NandhaKishorM/AI-Quadruped-Robot-For-Agriculture/screenshots/img5.gif

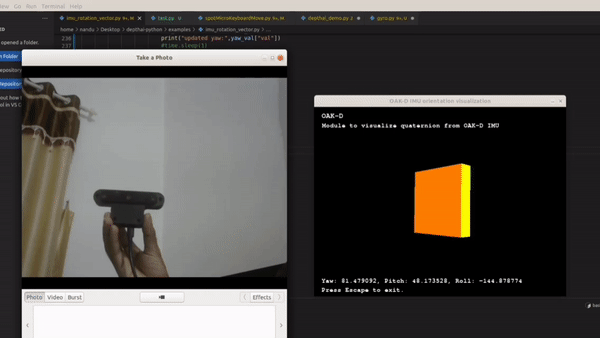
screenshots/img5.gif
