NandhaKishorM/AI-Quadruped-Robot-For-Agriculture/src/assets/1_robot_right_links.png

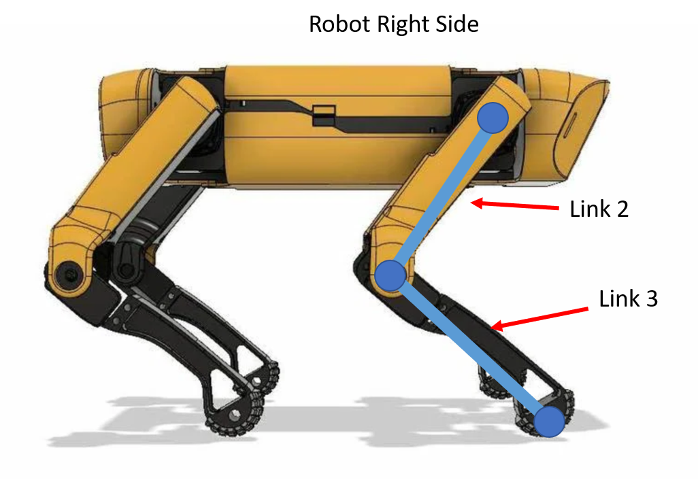
src/assets/1_robot_right_links.png
