NandhaKishorM/AI-Quadruped-Robot-For-Agriculture/src/assets/2_right_straight_links.png

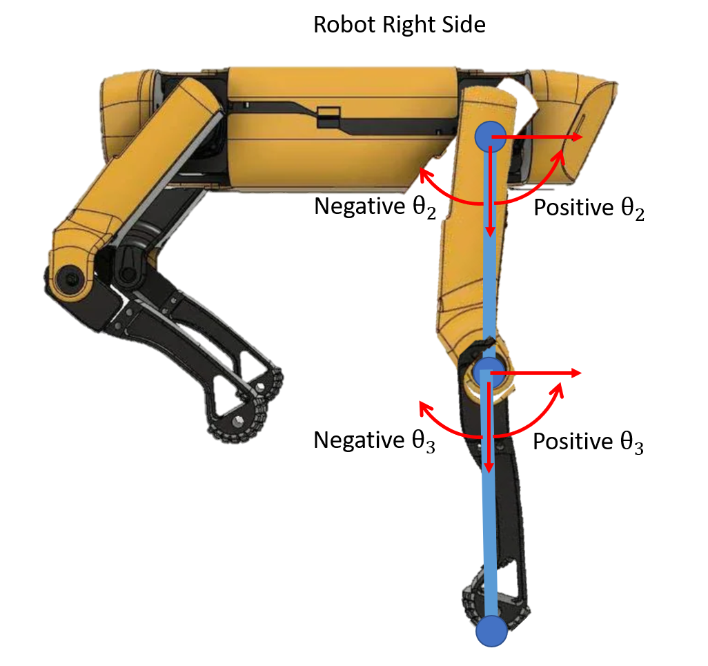
src/assets/2_right_straight_links.png
