NandhaKishorM/AI-Quadruped-Robot-For-Agriculture/src/assets/3_right_link_angles_example.png

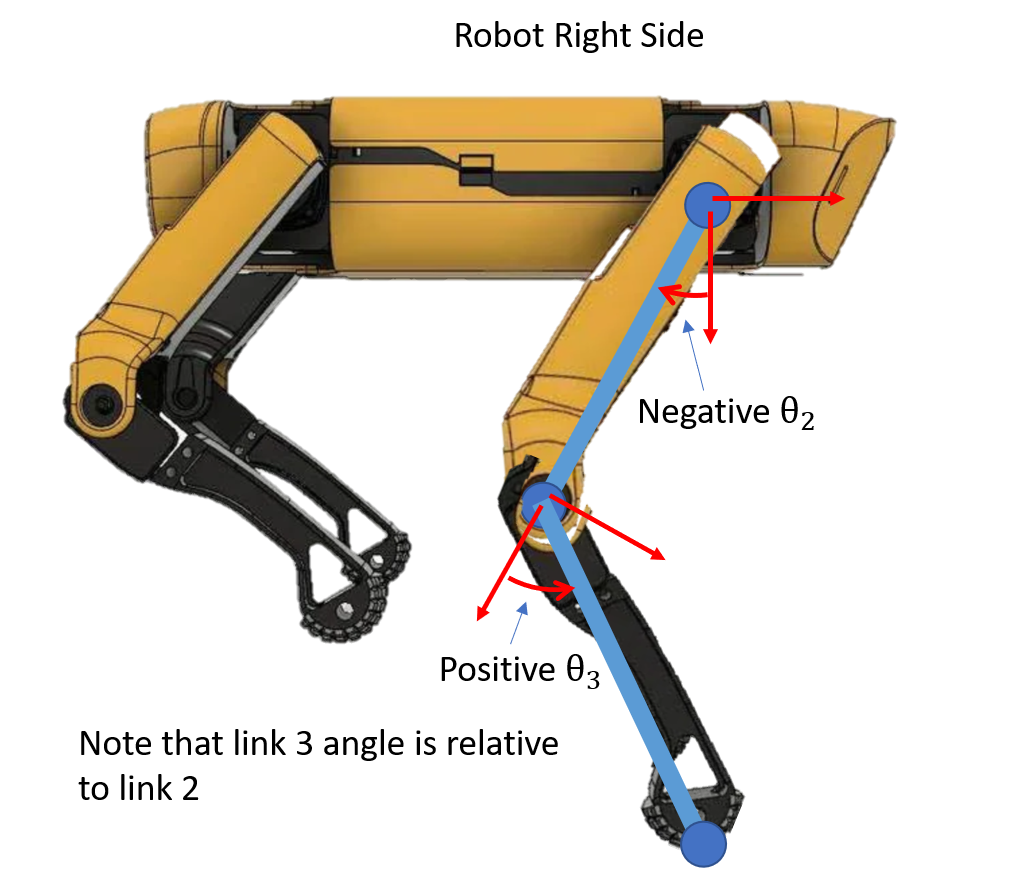
src/assets/3_right_link_angles_example.png
