NandhaKishorM/AI-Quadruped-Robot-For-Agriculture/src/assets/7_robot_left_overview.png

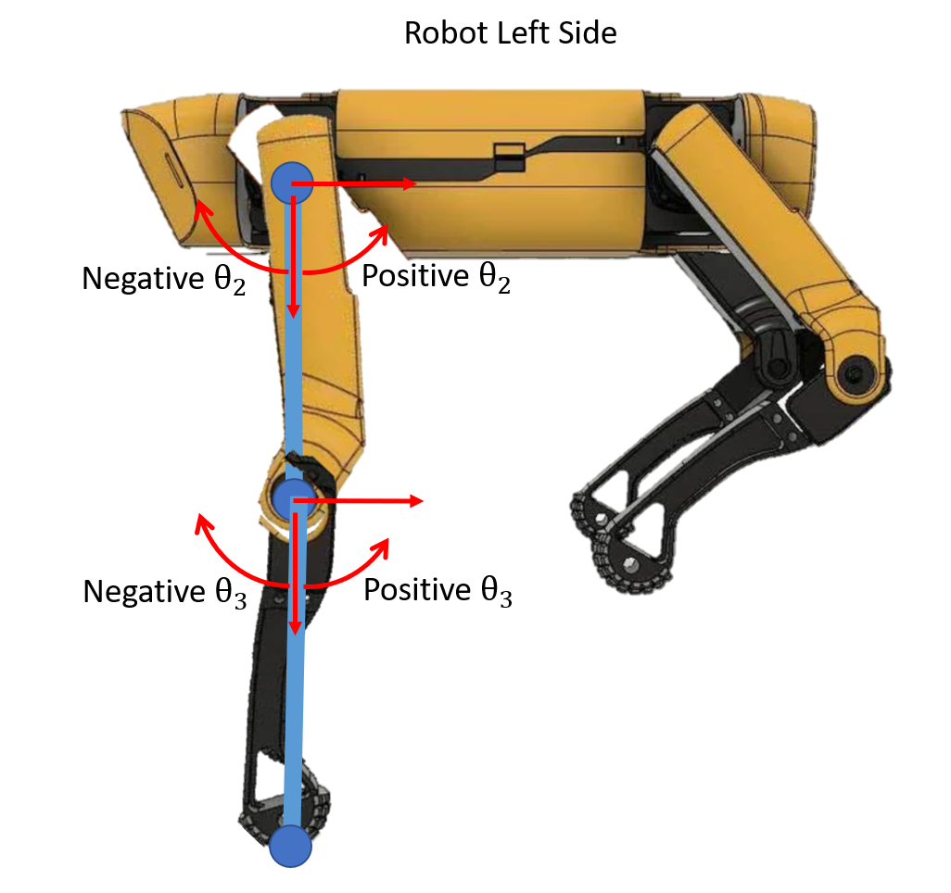
src/assets/7_robot_left_overview.png
