NandhaKishorM/AI-Quadruped-Robot-For-Agriculture/src/assets/12_robot_back_overview.png

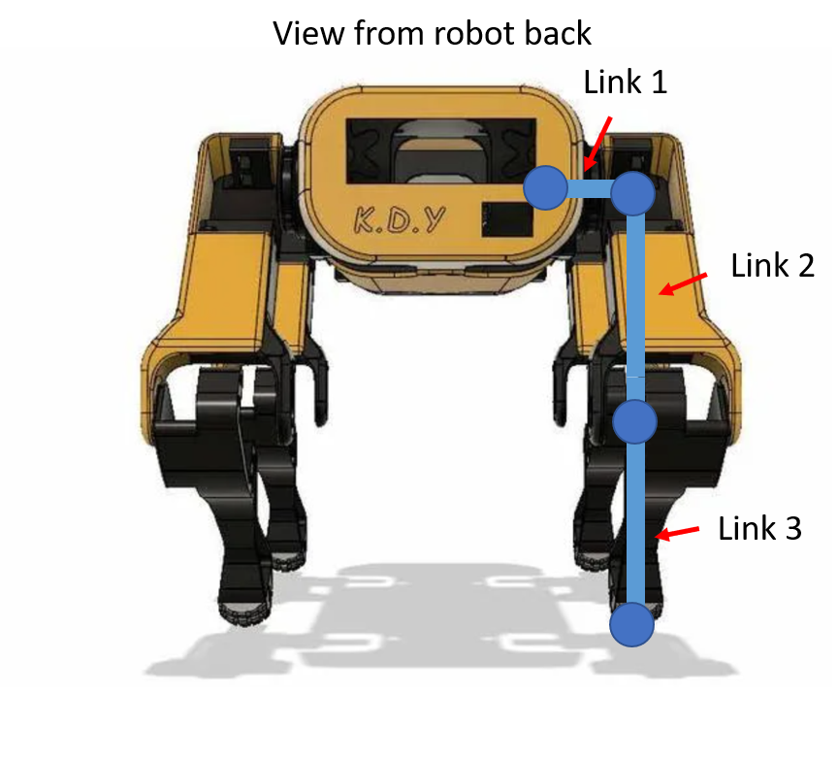
src/assets/12_robot_back_overview.png
