NandhaKishorM/AI-Quadruped-Robot-For-Agriculture/src/assets/kinematic_coord_system.jpg

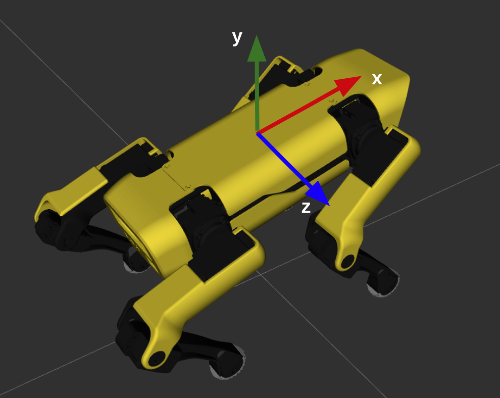
src/assets/kinematic_coord_system.jpg
