NandhaKishorM/AI-Quadruped-Robot-For-Agriculture/src/assets/lidar_mount.jpg

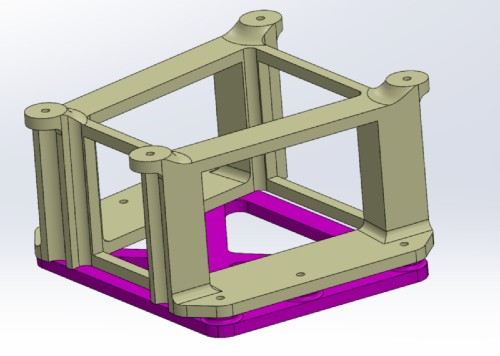
src/assets/lidar_mount.jpg
