NandhaKishorM/AI-Quadruped-Robot-For-Agriculture/src/assets/robot_bottom.jpg

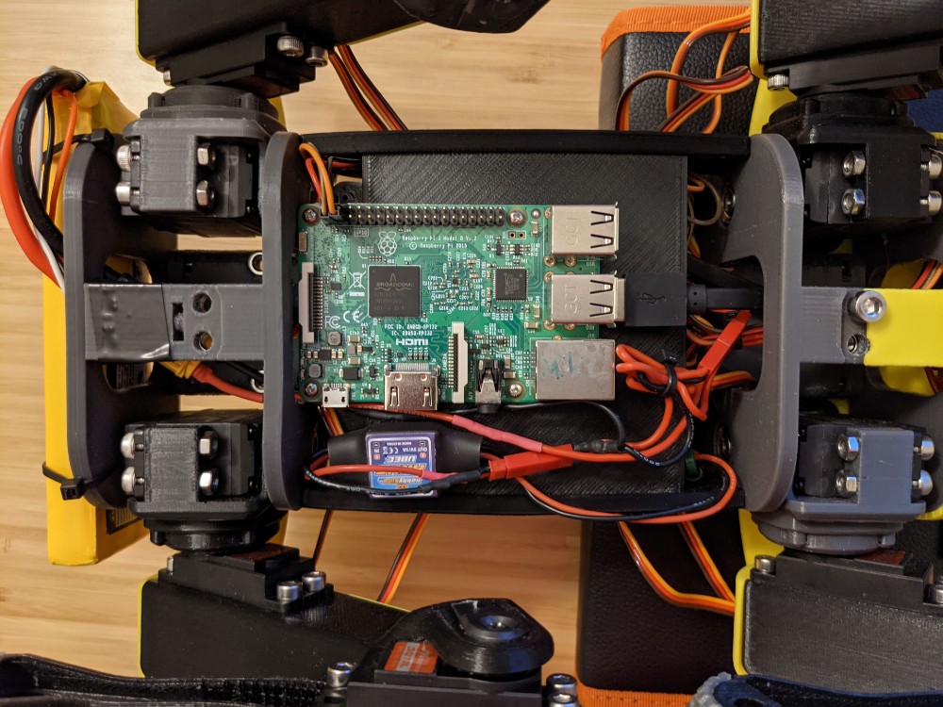
src/assets/robot_bottom.jpg
