NandhaKishorM/AI-Quadruped-Robot-For-Agriculture/src/assets/robot_top.jpg

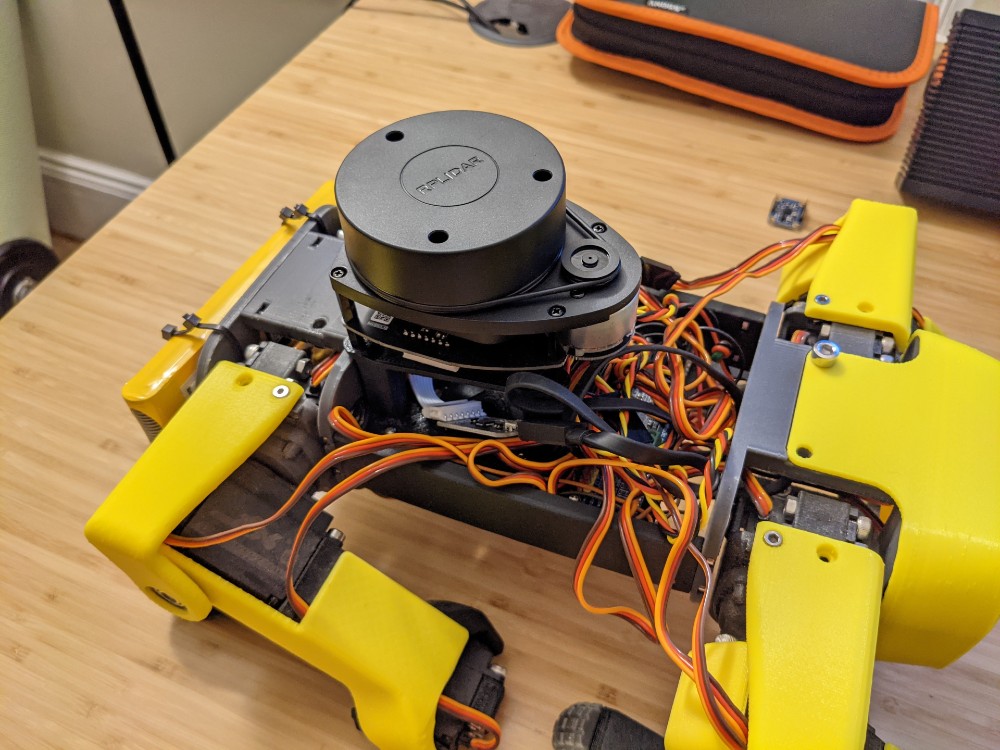
src/assets/robot_top.jpg
