NandhaKishorM/AI-Quadruped-Robot-For-Agriculture/src/assets/robot_top_no_servos.jpg

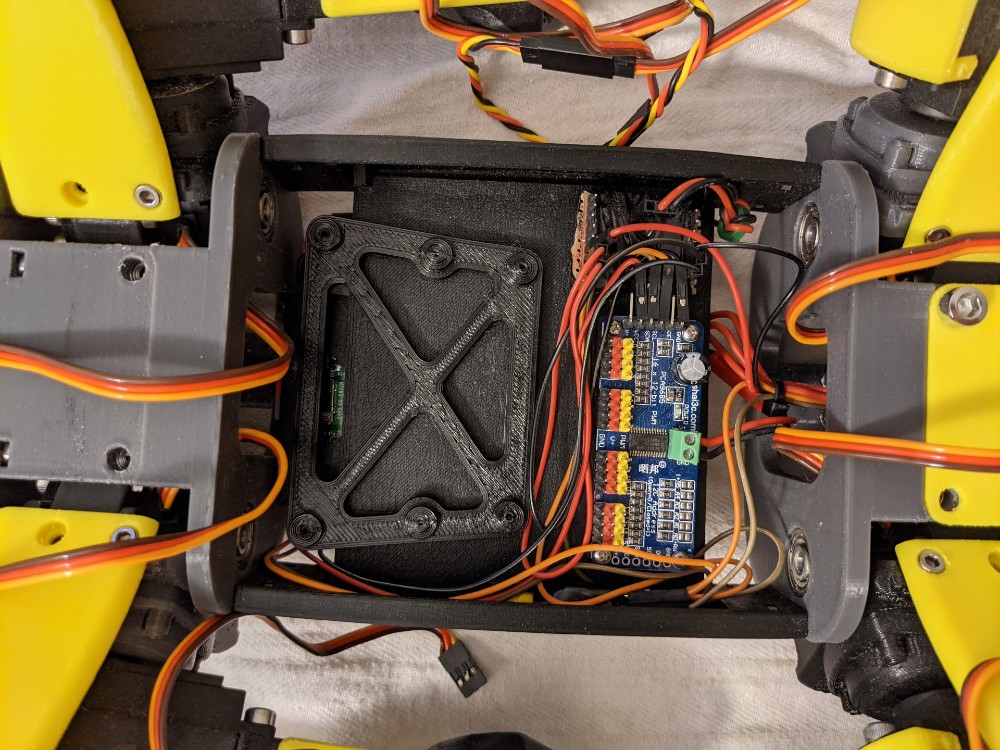
src/assets/robot_top_no_servos.jpg
