NandhaKishorM/AI-Quadruped-Robot-For-Agriculture/src/assets/rpi_platform.jpg

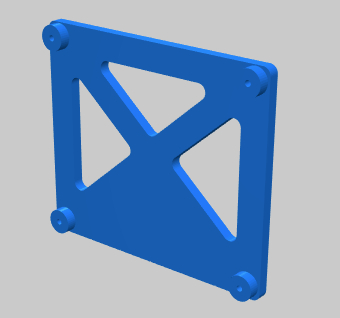
src/assets/rpi_platform.jpg
