NandhaKishorM/AI-Quadruped-Robot-For-Agriculture/src/assets/rviz_animation.gif

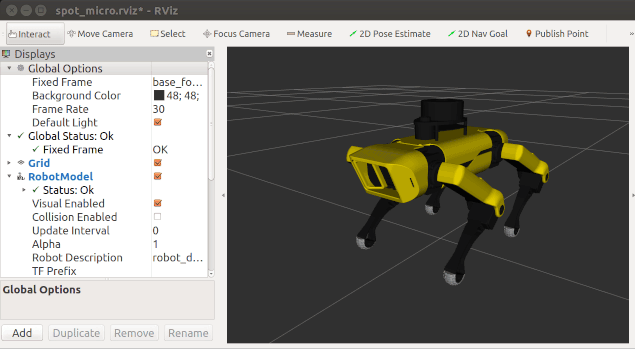
src/assets/rviz_animation.gif
