NandhaKishorM/AI-Quadruped-Robot-For-Agriculture/src/assets/servo_move_prompt.png

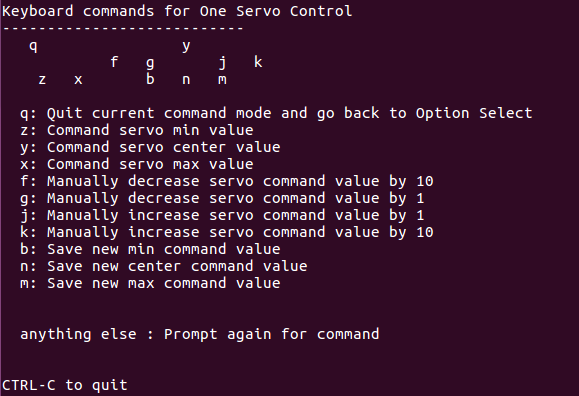
src/assets/servo_move_prompt.png
