NandhaKishorM/AI-Quadruped-Robot-For-Agriculture/src/assets/spot_micro_slam.gif

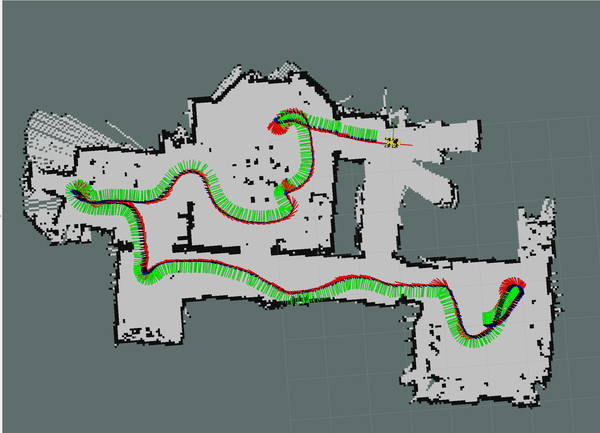
src/assets/spot_micro_slam.gif
