NandhaKishorM/AI-Quadruped-Robot-For-Agriculture/src/assets/state_machine.png

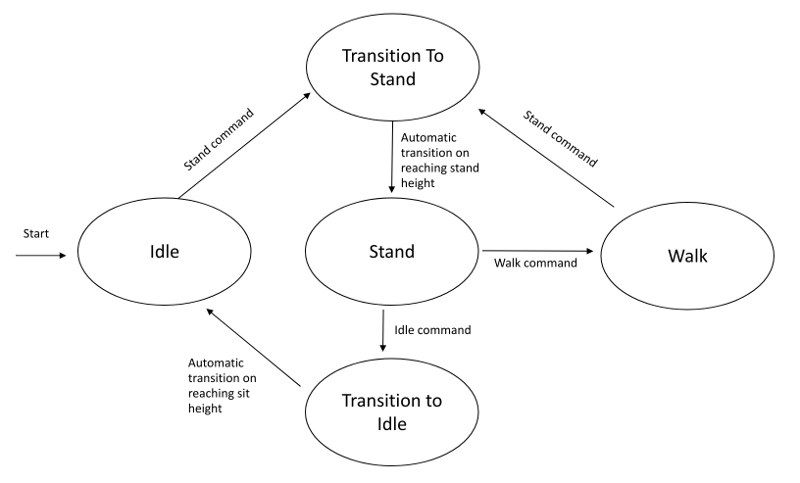
src/assets/state_machine.png
