NandhaKishorM/AI-Quadruped-Robot-For-Agriculture/src/assets/tf2_coord_system.jpg

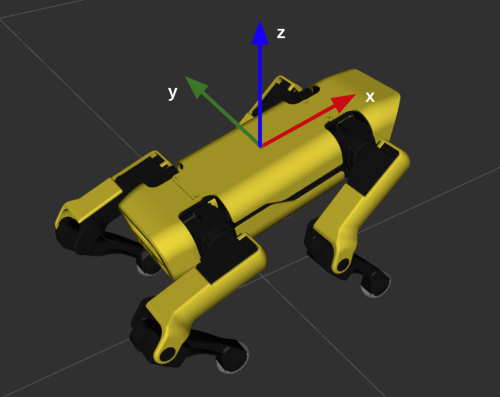
src/assets/tf2_coord_system.jpg
