NandhaKishorM/AI-Quadruped-Robot-For-Agriculture/src/spot_micro_plot/scripts/spot_micro_kinematics_python/assets/general_leg_geometry.png

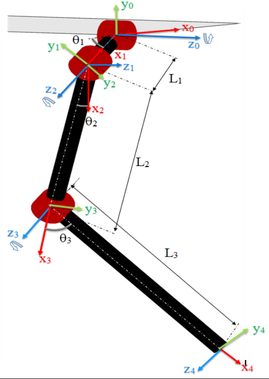
src/spot_micro_plot/scripts/spot_micro_kinematics_python/assets/general_leg_geometry.png
