NandhaKishorM/AI-Quadruped-Robot-For-Agriculture/Arm 3D print stl files/Forward Arm A.stl

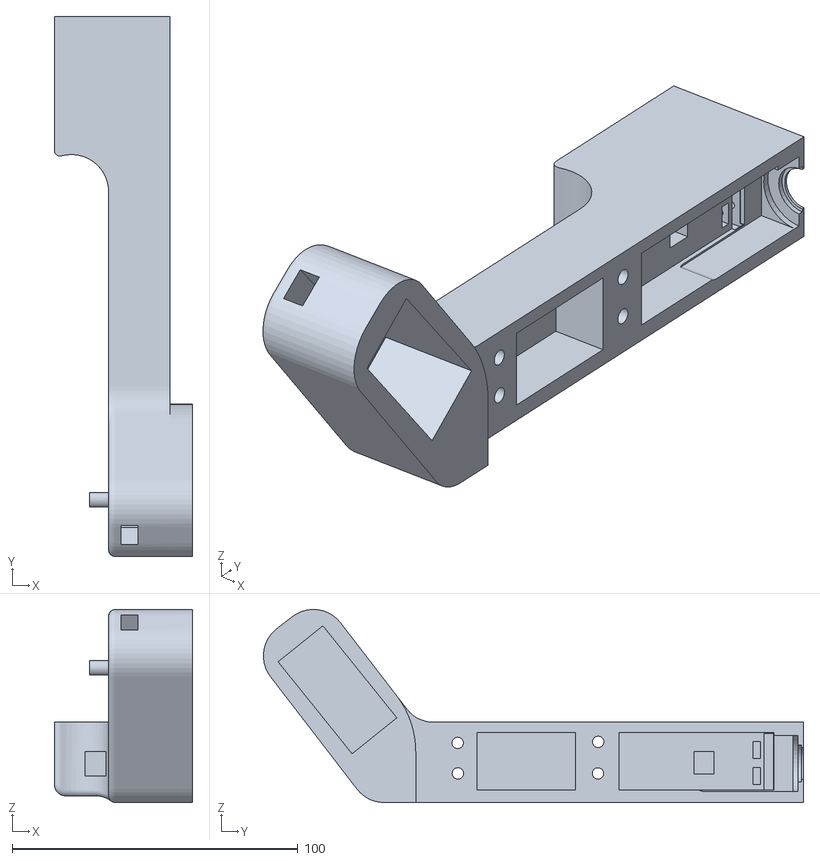
[picture p51: CAD file, 2021-08-09]
Arm 3D print stl files/Forward Arm A.stl
48.4 x 188.9 x 67.5
