NandhaKishorM/AI-Quadruped-Robot-For-Agriculture/Arm 3D print stl files/Head C.stl

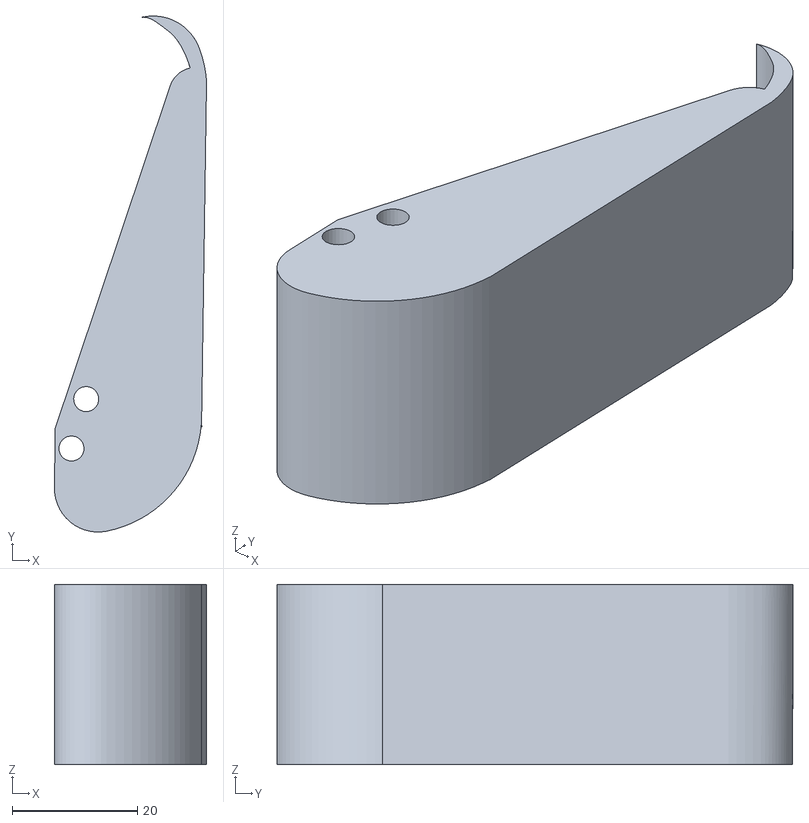
[picture p52: CAD file, 2021-08-09]
Arm 3D print stl files/Head C.stl
24.3 x 82.3 x 28.7
