NandhaKishorM/AI-Quadruped-Robot-For-Agriculture/src/spot_micro_rviz/urdf/stl/rarm.stl

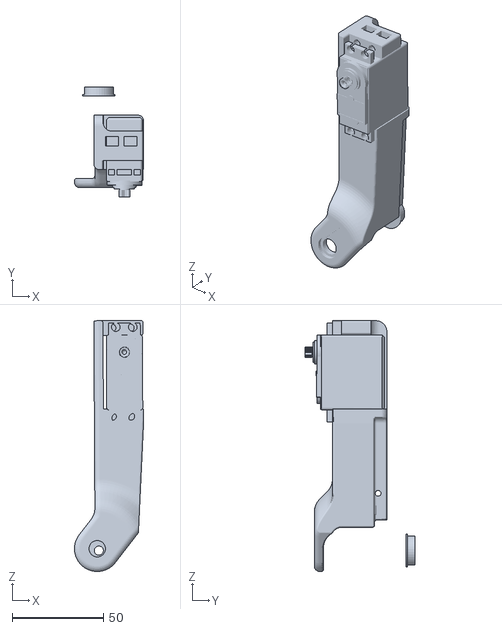
[picture p53: CAD file, 2021-07-23]
src/spot_micro_rviz/urdf/stl/rarm.stl
37.9 x 60.2 x 137.5
