NandhaKishorM/AI-Quadruped-Robot-For-Agriculture/Arm 3D print stl files/Arm 1.stl

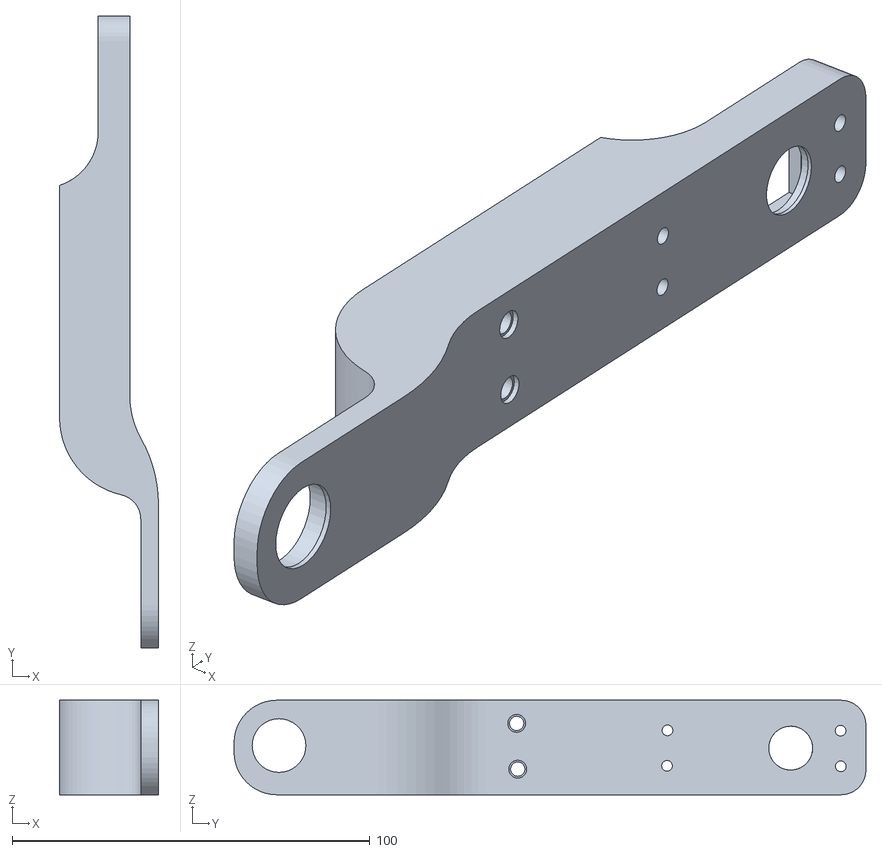
[picture p54: CAD file, 2021-08-09]
Arm 3D print stl files/Arm 1.stl
27.7 x 176.6 x 26.5
