NandhaKishorM/AI-Quadruped-Robot-For-Agriculture/Arm 3D print stl files/Forward Arm B.stl

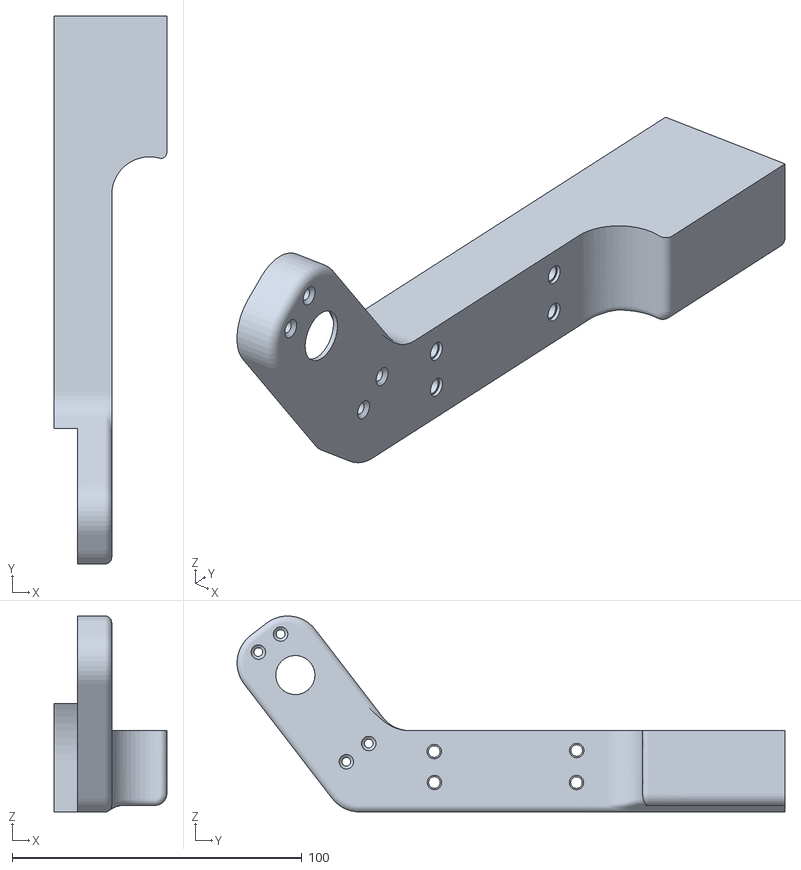
[picture p55: CAD file, 2021-08-09]
Arm 3D print stl files/Forward Arm B.stl
38.9 x 189.0 x 67.6
