NandhaKishorM/AI-Quadruped-Robot-For-Agriculture/src/spot_micro_rviz/urdf/stl/rfoot.stl

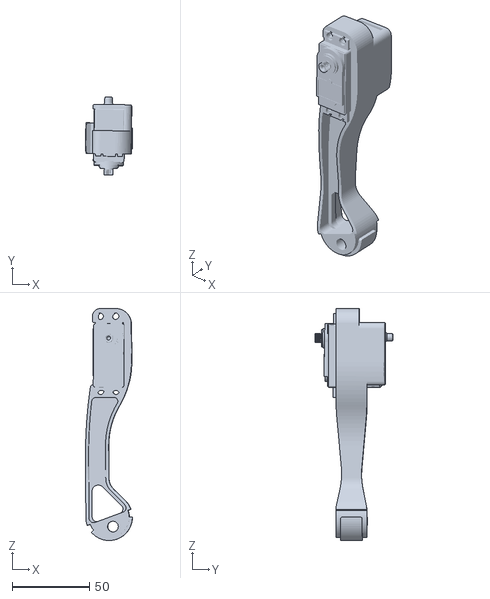
[picture p56: CAD file, 2021-07-23]
src/spot_micro_rviz/urdf/stl/rfoot.stl
30.4 x 50.7 x 150.0
