NandhaKishorM/AI-Quadruped-Robot-For-Agriculture/src/assets/4_right_link2_config_step_1.png

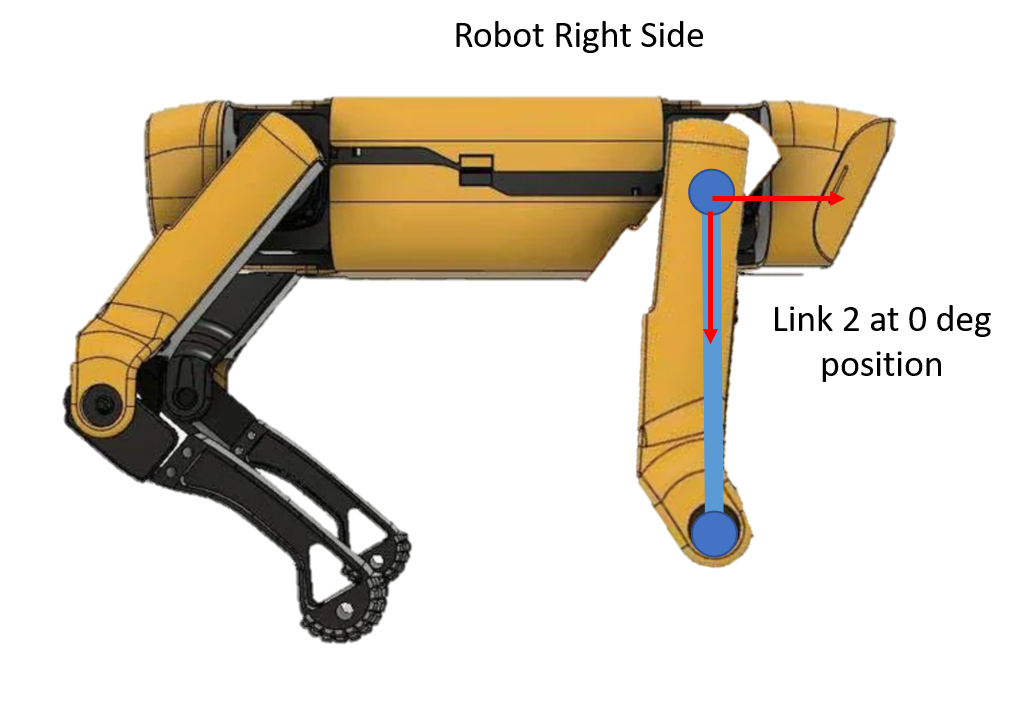
src/assets/4_right_link2_config_step_1.png
