NandhaKishorM/AI-Quadruped-Robot-For-Agriculture/src/assets/5_right_link3_config_step_1.png

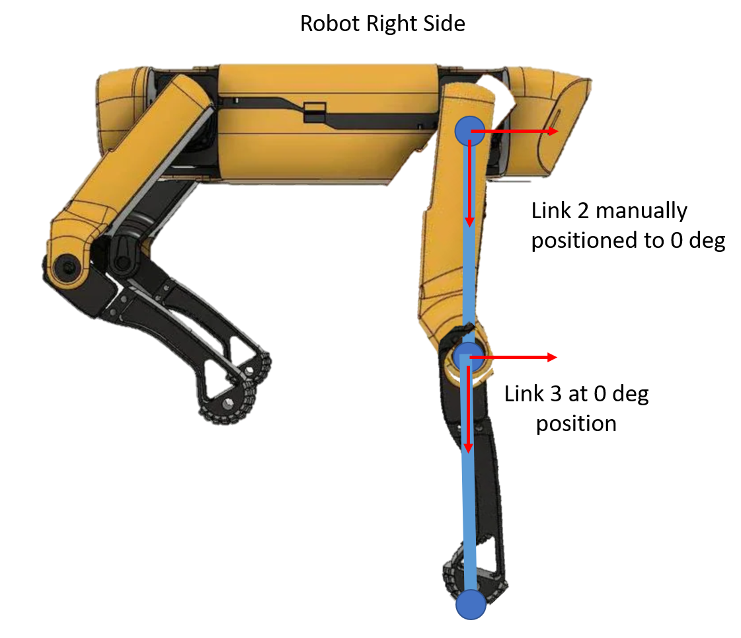
src/assets/5_right_link3_config_step_1.png
