NandhaKishorM/AI-Quadruped-Robot-For-Agriculture/src/assets/6_right_link3_config_step_2.png

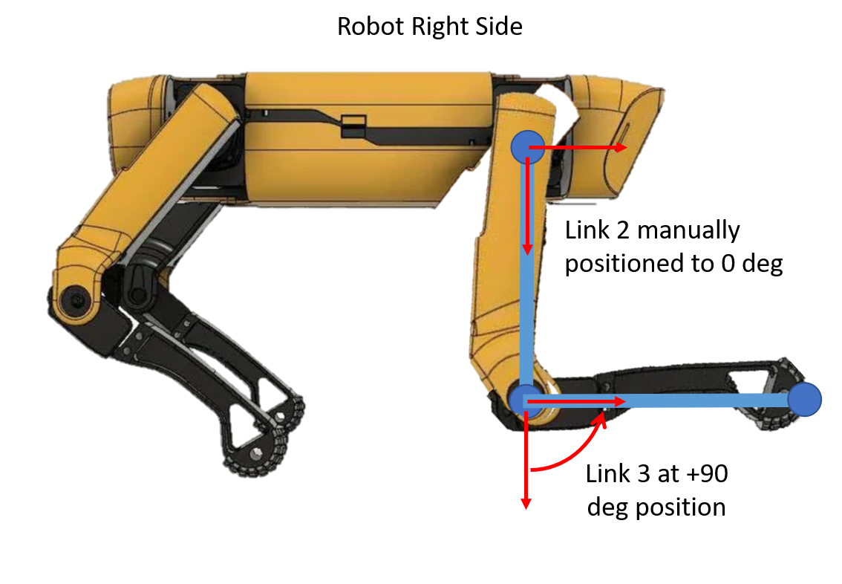
src/assets/6_right_link3_config_step_2.png
