NandhaKishorM/AI-Quadruped-Robot-For-Agriculture/src/assets/8_left_link2_config_step_1.png

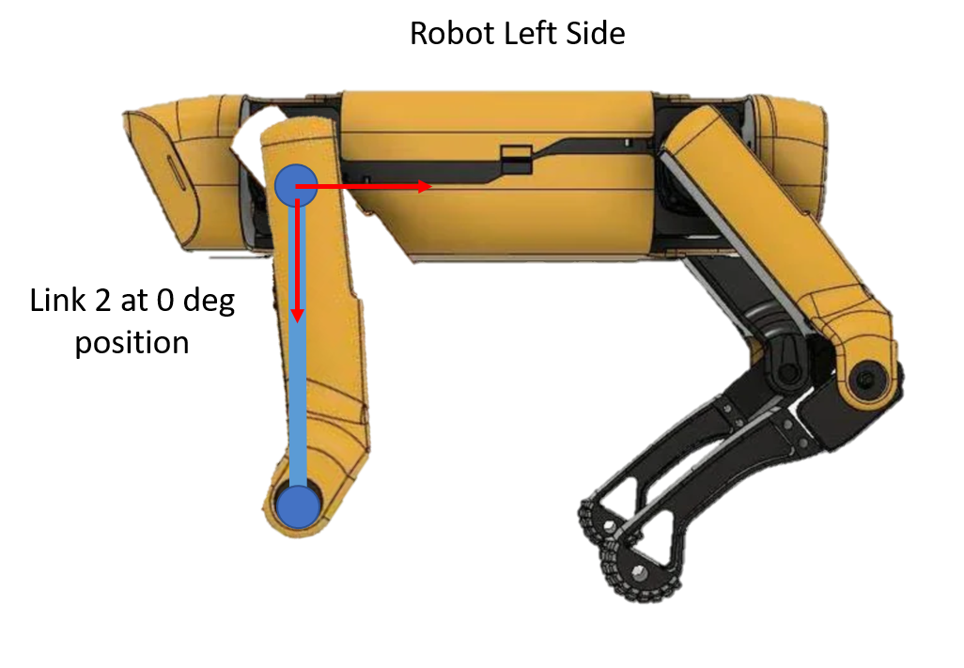
src/assets/8_left_link2_config_step_1.png
