NandhaKishorM/AI-Quadruped-Robot-For-Agriculture/src/assets/9_left_link2_config_step_2.png

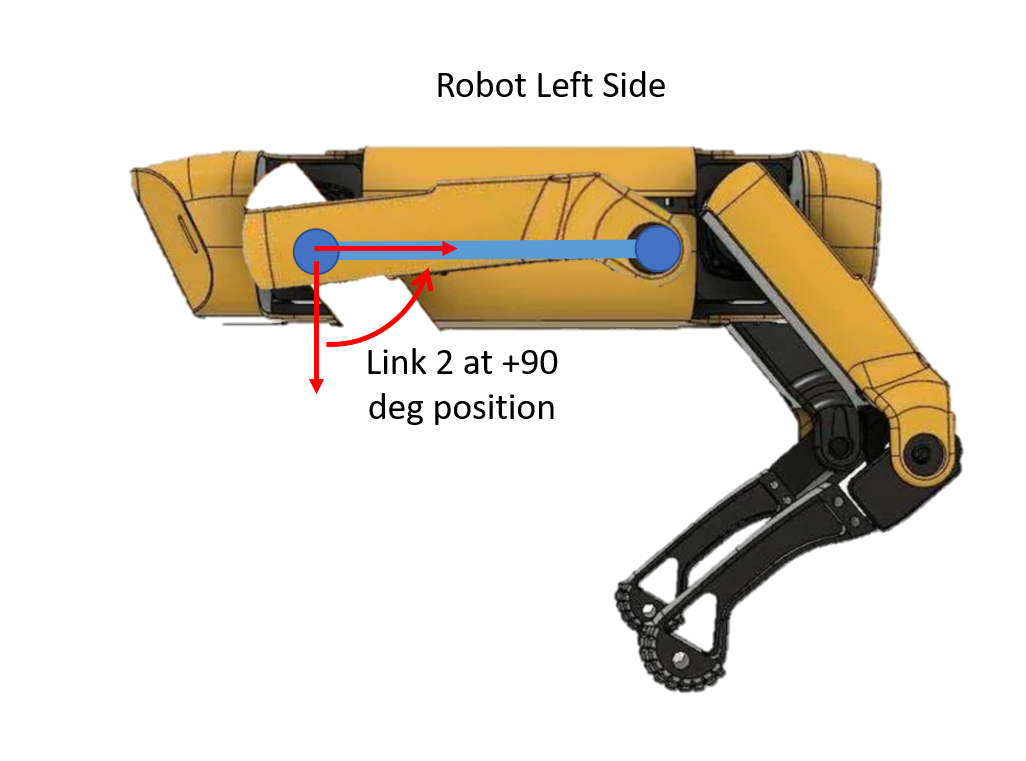
src/assets/9_left_link2_config_step_2.png
