NandhaKishorM/AI-Quadruped-Robot-For-Agriculture/src/assets/10_left_link3_config_step_1.png

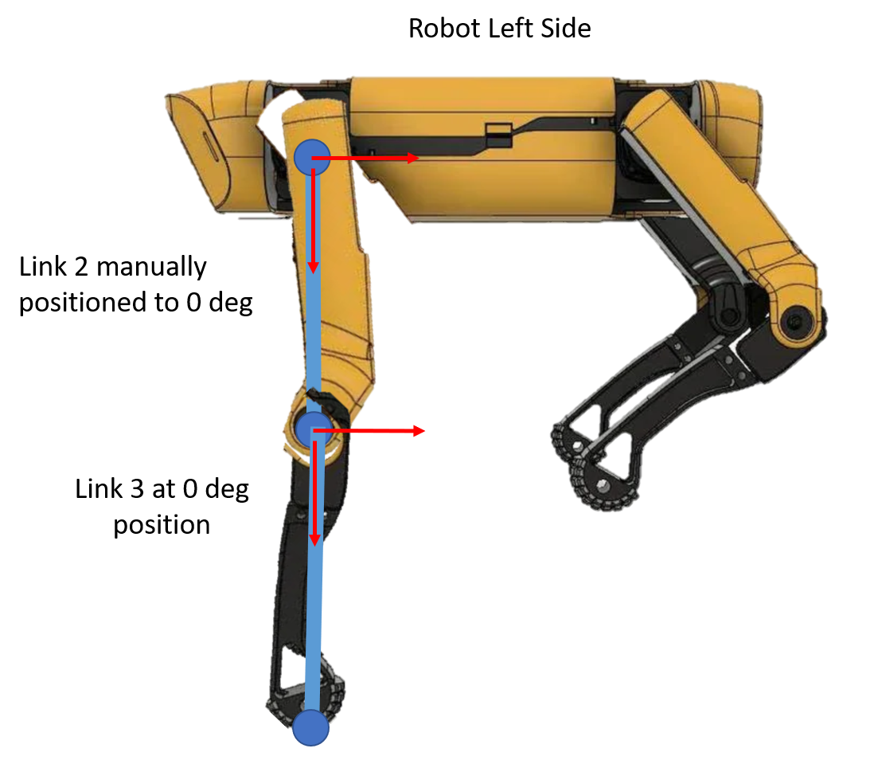
src/assets/10_left_link3_config_step_1.png
