NandhaKishorM/AI-Quadruped-Robot-For-Agriculture/src/assets/11_left_link3_config_step_2.png

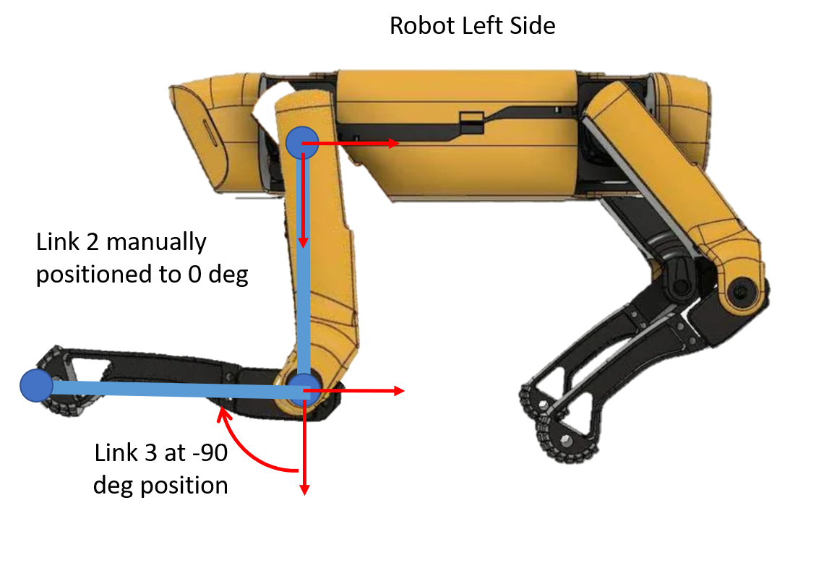
src/assets/11_left_link3_config_step_2.png
