NandhaKishorM/AI-Quadruped-Robot-For-Agriculture/src/assets/14_right_link1_config_step_1.png

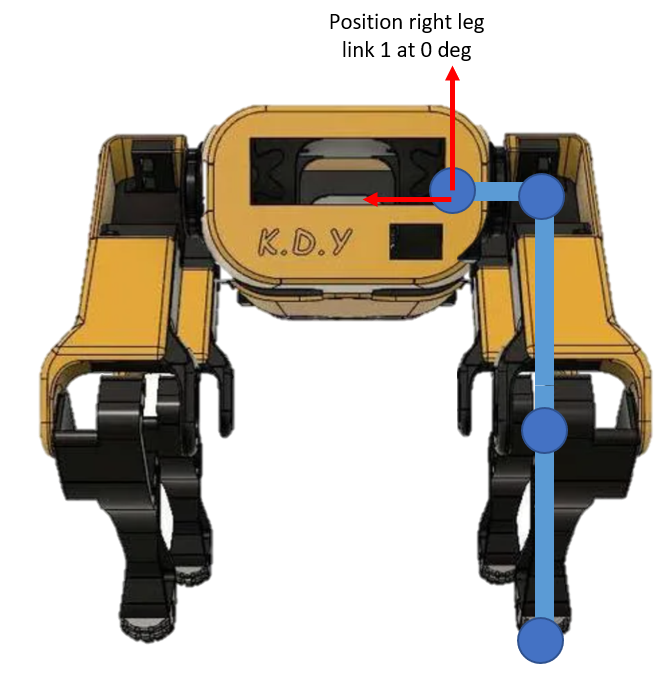
src/assets/14_right_link1_config_step_1.png
