NandhaKishorM/AI-Quadruped-Robot-For-Agriculture/src/assets/15_right_link1_config_step_2.png

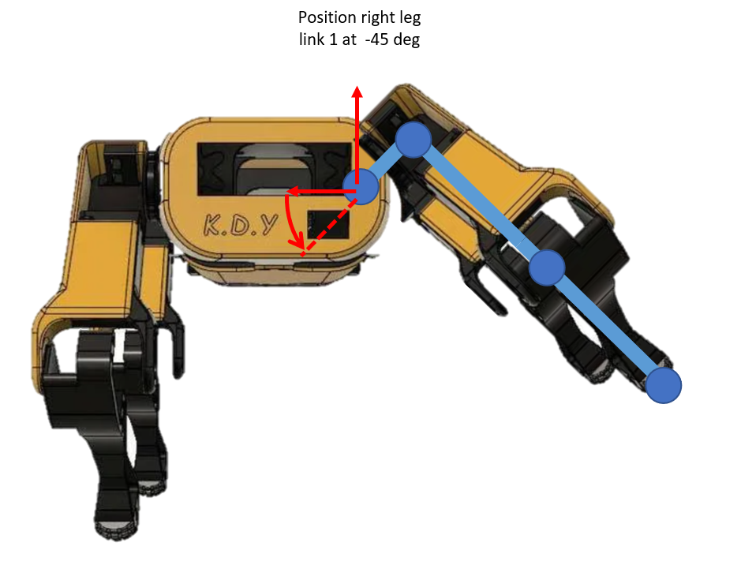
src/assets/15_right_link1_config_step_2.png
