NandhaKishorM/AI-Quadruped-Robot-For-Agriculture/src/assets/16_left_link1_config_step_1.png

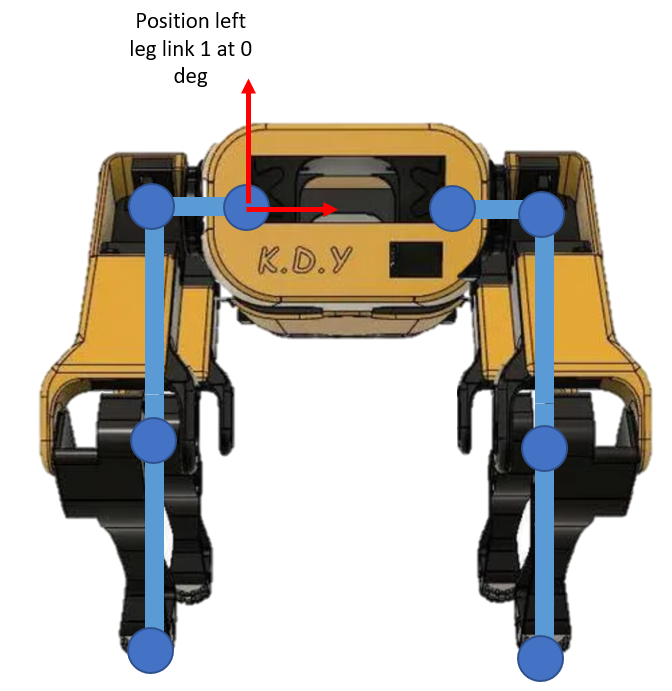
src/assets/16_left_link1_config_step_1.png
