NandhaKishorM/AI-Quadruped-Robot-For-Agriculture/src/assets/17_left_link1_config_step_2.png

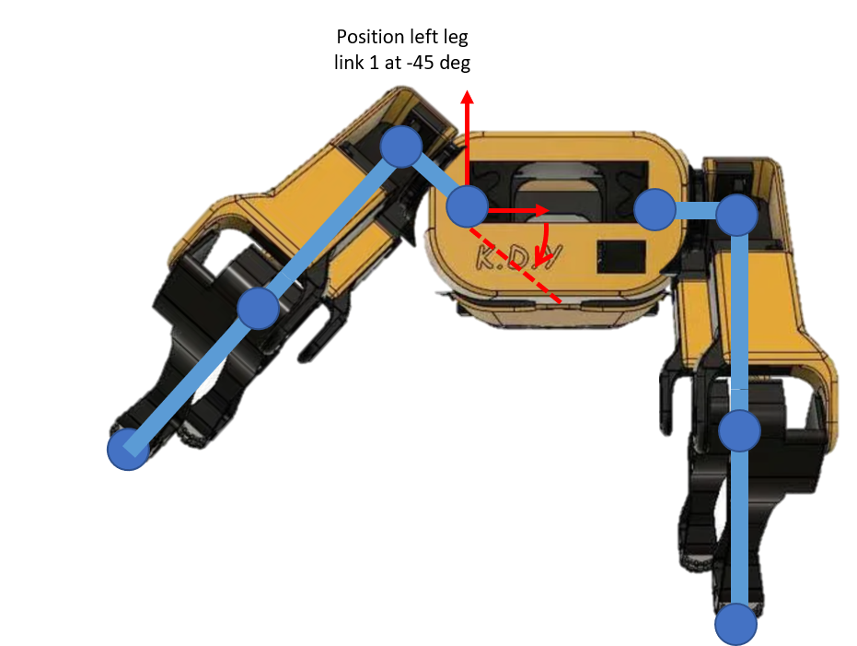
src/assets/17_left_link1_config_step_2.png
