NandhaKishorM/AI-Quadruped-Robot-For-Agriculture/src/assets/custom_shoulder_assembly.jpg

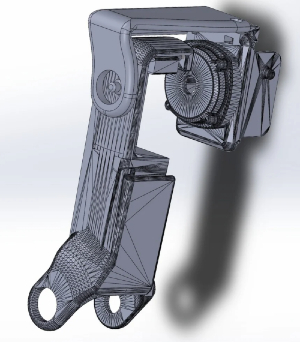
src/assets/custom_shoulder_assembly.jpg
