NandhaKishorM/AI-Quadruped-Robot-For-Agriculture/src/assets/servo_calibration_spreadsheet.png

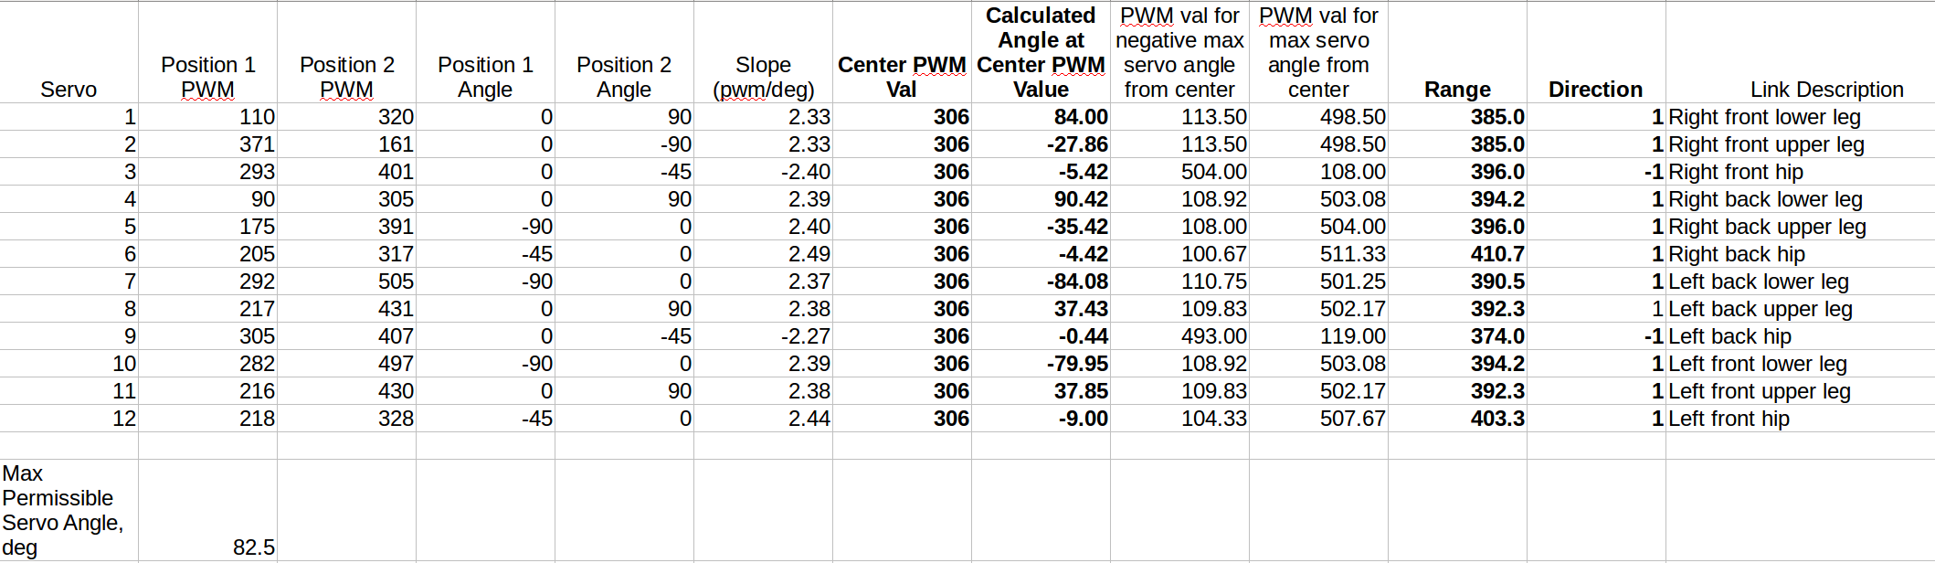
src/assets/servo_calibration_spreadsheet.png
