NandhaKishorM/AI-Quadruped-Robot-For-Agriculture/spatial_mobilenet.py

#!/usr/bin/env python3

from pathlib import Path
import sys
import cv2
import depthai as dai
import numpy as np
import time

'''
Spatial detection network demo.
    Performs inference on RGB camera and retrieves spatial location coordinates: x,y,z relative to the center of depth map.
'''

# Get argument first
nnBlobPath = str((Path(__file__).parent / Path('models/mobilenet-ssd_openvino_2021.2_8shave.blob')).resolve().absolute())
if len(sys.argv) > 1:
    nnBlobPath = sys.argv[1]


# MobilenetSSD label texts
labelMap = ["background", "aeroplane", "bicycle", "bird", "boat", "bottle", "bus", "car", "cat", "chair", "cow",
            "diningtable", "dog", "horse", "motorbike", "person", "pottedplant", "sheep", "sofa", "train", "tvmonitor"]

syncNN = True

# Create pipeline
pipeline = dai.Pipeline()

# Define sources and outputs
camRgb = pipeline.createColorCamera()
spatialDetectionNetwork = pipeline.createMobileNetSpatialDetectionNetwork()
monoLeft = pipeline.createMonoCamera()
monoRight = pipeline.createMonoCamera()
stereo = pipeline.createStereoDepth()

xoutRgb = pipeline.createXLinkOut()
xoutNN = pipeline.createXLinkOut()
xoutBoundingBoxDepthMapping = pipeline.createXLinkOut()
xoutDepth = pipeline.createXLinkOut()

xoutRgb.setStreamName("rgb")
xoutNN.setStreamName("detections")
xoutBoundingBoxDepthMapping.setStreamName("boundingBoxDepthMapping")
xoutDepth.setStreamName("depth")

# Properties
camRgb.setPreviewSize(300, 300)
camRgb.setResolution(dai.ColorCameraProperties.SensorResolution.THE_1080_P)
camRgb.setInterleaved(False)
camRgb.setColorOrder(dai.ColorCameraProperties.ColorOrder.BGR)

monoLeft.setResolution(dai.MonoCameraProperties.SensorResolution.THE_400_P)
monoLeft.setBoardSocket(dai.CameraBoardSocket.LEFT)
monoRight.setResolution(dai.MonoCameraProperties.SensorResolution.THE_400_P)
monoRight.setBoardSocket(dai.CameraBoardSocket.RIGHT)

# Setting node configs
stereo.initialConfig.setConfidenceThreshold(255)

spatialDetectionNetwork.setBlobPath(nnBlobPath)
spatialDetectionNetwork.setConfidenceThreshold(0.5)
spatialDetectionNetwork.input.setBlocking(False)
spatialDetectionNetwork.setBoundingBoxScaleFactor(0.5)
spatialDetectionNetwork.setDepthLowerThreshold(100)
spatialDetectionNetwork.setDepthUpperThreshold(5000)

# Linking
monoLeft.out.link(stereo.left)
monoRight.out.link(stereo.right)

camRgb.preview.link(spatialDetectionNetwork.input)
if syncNN:
    spatialDetectionNetwork.passthrough.link(xoutRgb.input)
else:
    camRgb.preview.link(xoutRgb.input)

spatialDetectionNetwork.out.link(xoutNN.input)
spatialDetectionNetwork.boundingBoxMapping.link(xoutBoundingBoxDepthMapping.input)

stereo.depth.link(spatialDetectionNetwork.inputDepth)
spatialDetectionNetwork.passthroughDepth.link(xoutDepth.input)

# Connect to device and start pipeline
with dai.Device(pipeline) as device:

    # Output queues will be used to get the rgb frames and nn data from the outputs defined above
    previewQueue = device.getOutputQueue(name="rgb", maxSize=4, blocking=False)
    detectionNNQueue = device.getOutputQueue(name="detections", maxSize=4, blocking=False)
    xoutBoundingBoxDepthMapping = device.getOutputQueue(name="boundingBoxDepthMapping", maxSize=4, blocking=False)
    depthQueue = device.getOutputQueue(name="depth", maxSize=4, blocking=False)

    startTime = time.monotonic()
    counter = 0
    fps = 0

    while True:
        inPreview = previewQueue.get()
        inDet = detectionNNQueue.get()
        depth = depthQueue.get()

        counter+=1
        current_time = time.monotonic()
        if (current_time - startTime) > 1 :
            fps = counter / (current_time - startTime)
            counter = 0
            startTime = current_time

        frame = inPreview.getCvFrame()
        depthFrame = depth.getFrame()

        depthFrameColor = cv2.normalize(depthFrame, None, 255, 0, cv2.NORM_INF, cv2.CV_8UC1)
        depthFrameColor = cv2.equalizeHist(depthFrameColor)
        depthFrameColor = cv2.applyColorMap(depthFrameColor, cv2.COLORMAP_HOT)

        detections = inDet.detections
        if len(detections) != 0:
            boundingBoxMapping = xoutBoundingBoxDepthMapping.get()
            roiDatas = boundingBoxMapping.getConfigData()

            for roiData in roiDatas:
                roi = roiData.roi
                roi = roi.denormalize(depthFrameColor.shape[1], depthFrameColor.shape[0])
                topLeft = roi.topLeft()
                bottomRight = roi.bottomRight()
                xmin = int(topLeft.x)
                ymin = int(topLeft.y)
                xmax = int(bottomRight.x)
                ymax = int(bottomRight.y)

                cv2.rectangle(depthFrameColor, (xmin, ymin), (xmax, ymax), 255, cv2.FONT_HERSHEY_SCRIPT_SIMPLEX)

        # If the frame is available, draw bounding boxes on it and show the frame
        height = frame.shape[0]
        width  = frame.shape[1]
        for detection in detections:
            # Denormalize bounding box
            x1 = int(detection.xmin * width)
            x2 = int(detection.xmax * width)
            y1 = int(detection.ymin * height)
            y2 = int(detection.ymax * height)
            try:
                label = labelMap[detection.label]
            except:
                label = detection.label
            cv2.putText(frame, str(label), (x1 + 10, y1 + 20), cv2.FONT_HERSHEY_TRIPLEX, 0.5, 255)
            cv2.putText(frame, "{:.2f}".format(detection.confidence*100), (x1 + 10, y1 + 35), cv2.FONT_HERSHEY_TRIPLEX, 0.5, 255)
            cv2.putText(frame, f"X: {int(detection.spatialCoordinates.x)} mm", (x1 + 10, y1 + 50), cv2.FONT_HERSHEY_TRIPLEX, 0.5, 255)
            cv2.putText(frame, f"Y: {int(detection.spatialCoordinates.y)} mm", (x1 + 10, y1 + 65), cv2.FONT_HERSHEY_TRIPLEX, 0.5, 255)
            cv2.putText(frame, f"Z: {int(detection.spatialCoordinates.z)} mm", (x1 + 10, y1 + 80), cv2.FONT_HERSHEY_TRIPLEX, 0.5, 255)

            cv2.rectangle(frame, (x1, y1), (x2, y2), (255, 0, 0), cv2.FONT_HERSHEY_SIMPLEX)

        cv2.putText(frame, "NN fps: {:.2f}".format(fps), (2, frame.shape[0] - 4), cv2.FONT_HERSHEY_TRIPLEX, 0.4, (255,255,255))
        cv2.imshow("depth", depthFrameColor)
        cv2.imshow("preview", frame)

        if cv2.waitKey(1) == ord('q'):
            break
