NandhaKishorM/AI-Quadruped-Robot-For-Agriculture/gyro_visualization.py

#!/usr/bin/env python3

from itertools import count
import cv2
import depthai as dai
import numpy
import time
import math
import pygame
import math
from OpenGL.GL import *
from OpenGL.GLU import *
from pygame.locals import *

d = {'w': 0, 'x': 0, 'y': 0,'z':0}

def resizewin(width, height):
    """
    For resizing window
    """
    if height == 0:
        height = 1
    glViewport(0, 0, width, height)
    glMatrixMode(GL_PROJECTION)
    glLoadIdentity()
    gluPerspective(45, 1.0*width/height, 0.1, 100.0)
    glMatrixMode(GL_MODELVIEW)
    glLoadIdentity()


def init():
    glShadeModel(GL_SMOOTH)
    glClearColor(0.0, 0.0, 0.0, 0.0)
    glClearDepth(1.0)
    glEnable(GL_DEPTH_TEST)
    glDepthFunc(GL_LEQUAL)
    glHint(GL_PERSPECTIVE_CORRECTION_HINT, GL_NICEST)






def draw(w, nx, ny, nz):
    glClear(GL_COLOR_BUFFER_BIT | GL_DEPTH_BUFFER_BIT)
    glLoadIdentity()
    glTranslatef(0, 0.0, -7.0)

    drawText((-2.6, 1.8, 2), "OAK-D", 18)
    drawText((-2.6, 1.6, 2), "Module to visualize quaternion from OAK-D IMU", 16)
    drawText((-2.6, -2, 2), "Press Escape to exit.", 16)

    [yaw, pitch , roll] = quat_to_ypr([w, nx, ny, nz])
   

   
    drawText((-2.6, -1.8, 2), "Yaw: %f, Pitch: %f, Roll: %f" %(yaw, pitch, roll), 16)
    glRotatef(2 * math.acos(w) * 180.00/math.pi, -1 * nx, nz, ny)
   

    glBegin(GL_QUADS)
    glColor3f(0.0, 1.0, 0.0)
    glVertex3f(1.0, 0.2, -1.0)
    glVertex3f(-1.0, 0.2, -1.0)
    glVertex3f(-1.0, 0.2, 1.0)
    glVertex3f(1.0, 0.2, 1.0)

    glColor3f(1.0, 0.5, 0.0)
    glVertex3f(1.0, -0.2, 1.0)
    glVertex3f(-1.0, -0.2, 1.0)
    glVertex3f(-1.0, -0.2, -1.0)
    glVertex3f(1.0, -0.2, -1.0)

    glColor3f(1.0, 0.0, 0.0)
    glVertex3f(1.0, 0.2, 1.0)
    glVertex3f(-1.0, 0.2, 1.0)
    glVertex3f(-1.0, -0.2, 1.0)
    glVertex3f(1.0, -0.2, 1.0)

    glColor3f(1.0, 1.0, 0.0)
    glVertex3f(1.0, -0.2, -1.0)
    glVertex3f(-1.0, -0.2, -1.0)
    glVertex3f(-1.0, 0.2, -1.0)
    glVertex3f(1.0, 0.2, -1.0)

    glColor3f(0.0, 0.0, 1.0)
    glVertex3f(-1.0, 0.2, 1.0)
    glVertex3f(-1.0, 0.2, -1.0)
    glVertex3f(-1.0, -0.2, -1.0)
    glVertex3f(-1.0, -0.2, 1.0)

    glColor3f(1.0, 0.0, 1.0)
    glVertex3f(1.0, 0.2, -1.0)
    glVertex3f(1.0, 0.2, 1.0)
    glVertex3f(1.0, -0.2, 1.0)
    glVertex3f(1.0, -0.2, -1.0)
    glEnd()


def drawText(position, textString, size):
    font = pygame.font.SysFont("Courier", size, True)
    textSurface = font.render(textString, True, (255, 255, 255, 255), (0, 0, 0, 255))
    textData = pygame.image.tostring(textSurface, "RGBA", True)
    glRasterPos3d(*position)
    glDrawPixels(textSurface.get_width(), textSurface.get_height(), GL_RGBA, GL_UNSIGNED_BYTE, textData)

def quat_to_ypr(q):
    yaw   = math.atan2(2.0 * (q[1] * q[2] + q[0] * q[3]), q[0] * q[0] + q[1] * q[1] - q[2] * q[2] - q[3] * q[3])
    pitch = -math.sin(2.0 * (q[1] * q[3] - q[0] * q[2]))
    roll  = math.atan2(2.0 * (q[0] * q[1] + q[2] * q[3]), q[0] * q[0] - q[1] * q[1] - q[2] * q[2] + q[3] * q[3])
    pitch *= 180.0 / math.pi
    yaw   *= 180.0 / math.pi
    yaw   -= -1.31  # Declination at Pilicode, Kerala is - 1 degress 31 min
    roll  *= 180.0 / math.pi
    return [yaw, pitch, roll]
def diff(q):
    yaw   = math.atan2(2.0 * (q[1] * q[2] + q[0] * q[3]), q[0] * q[0] + q[1] * q[1] - q[2] * q[2] - q[3] * q[3])
    pitch = -math.sin(2.0 * (q[1] * q[3] - q[0] * q[2]))
    roll  = math.atan2(2.0 * (q[0] * q[1] + q[2] * q[3]), q[0] * q[0] - q[1] * q[1] - q[2] * q[2] + q[3] * q[3])
    pitch *= 180.0 / math.pi
    yaw   *= 180.0 / math.pi
    yaw   -= -1.31  # Declination at Pilicode, Kerala is - 1 degress 31 min
    roll  *= 180.0 / math.pi
    
    
    return [yaw,pitch,roll]


# Create pipeline
pipeline = dai.Pipeline()

# Define sources and outputs
imu = pipeline.createIMU()
xlinkOut = pipeline.createXLinkOut()

xlinkOut.setStreamName("imu")

# enable ROTATION_VECTOR at 400 hz rate
imu.enableIMUSensor(dai.IMUSensor.ROTATION_VECTOR, 400)
# above this threshold packets will be sent in batch of X, if the host is not blocked and USB bandwidth is available
imu.setBatchReportThreshold(1)
# maximum number of IMU packets in a batch, if it's reached device will block sending until host can receive it
# if lower or equal to batchReportThreshold then the sending is always blocking on device
# useful to reduce device's CPU load  and number of lost packets, if CPU load is high on device side due to multiple nodes
imu.setMaxBatchReports(10)

# Link plugins IMU -> XLINK
imu.out.link(xlinkOut.input)

# Pipeline is defined, now we can connect to the device
with dai.Device(pipeline) as device:

    def timeDeltaToMilliS(delta) -> float:
        return delta.total_seconds()*1000

    # Output queue for imu bulk packets
    imuQueue = device.getOutputQueue(name="imu", maxSize=50, blocking=False)
    baseTs = None

    while True:
        imuData = imuQueue.get()  # blocking call, will wait until a new data has arrived

        imuPackets = imuData.packets
        for imuPacket in imuPackets:
            rVvalues = imuPacket.rotationVector

            rvTs = rVvalues.timestamp.get()
            if baseTs is None:
                baseTs = rvTs
            rvTs = rvTs - baseTs

            imuF = "{:.06f}"
            tsF  = "{:.03f}"

            print(f"Rotation vector timestamp: {tsF.format(timeDeltaToMilliS(rvTs))} ms")
            print(f"Quaternion: i: {imuF.format(rVvalues.i)} j: {imuF.format(rVvalues.j)} "
                f"k: {imuF.format(rVvalues.k)} real: {imuF.format(rVvalues.real)}")
            print(f"Accuracy (rad): {imuF.format(rVvalues.accuracy)}")

            d.update({'w':float("{0:.06f}".format(rVvalues.real)),'x':float("{0:.06f}".format(rVvalues.i)),'y':float("{0:.06f}".format(rVvalues.j)),'z':float("{0:.06}".format(rVvalues.k))})
            video_flags = OPENGL | DOUBLEBUF
            
            pygame.init()
            screen = pygame.display.set_mode((640, 480), video_flags)
            pygame.display.set_caption("OAK-D IMU orientation visualization")
            resizewin(640, 480)
            init()
            frames = 0
            ticks = pygame.time.get_ticks()
           
            event = pygame.event.poll()

  
        
            w = d["w"]
            x = d["x"]
            y = d["y"]
            z = d["z"]
     
          
           


            draw(w, x, y, z)
        
            pygame.display.flip()
            frames += 1
            #time.sleep(0.5)
        if event.type == QUIT or (event.type == KEYDOWN and event.key == K_ESCAPE):
            break
        
            #print("fps: %d" % ((frames*1000)/(pygame.time.get_ticks()-ticks)))
     
            
